cbalint13/e-verest/hardware/everest_v1.5/kicad/e-verest/e-verest.kicad_sch

## KiCad design hardware/everest_v1.5/kicad/e-verest/e-verest.kicad_sch (2021-08-18)

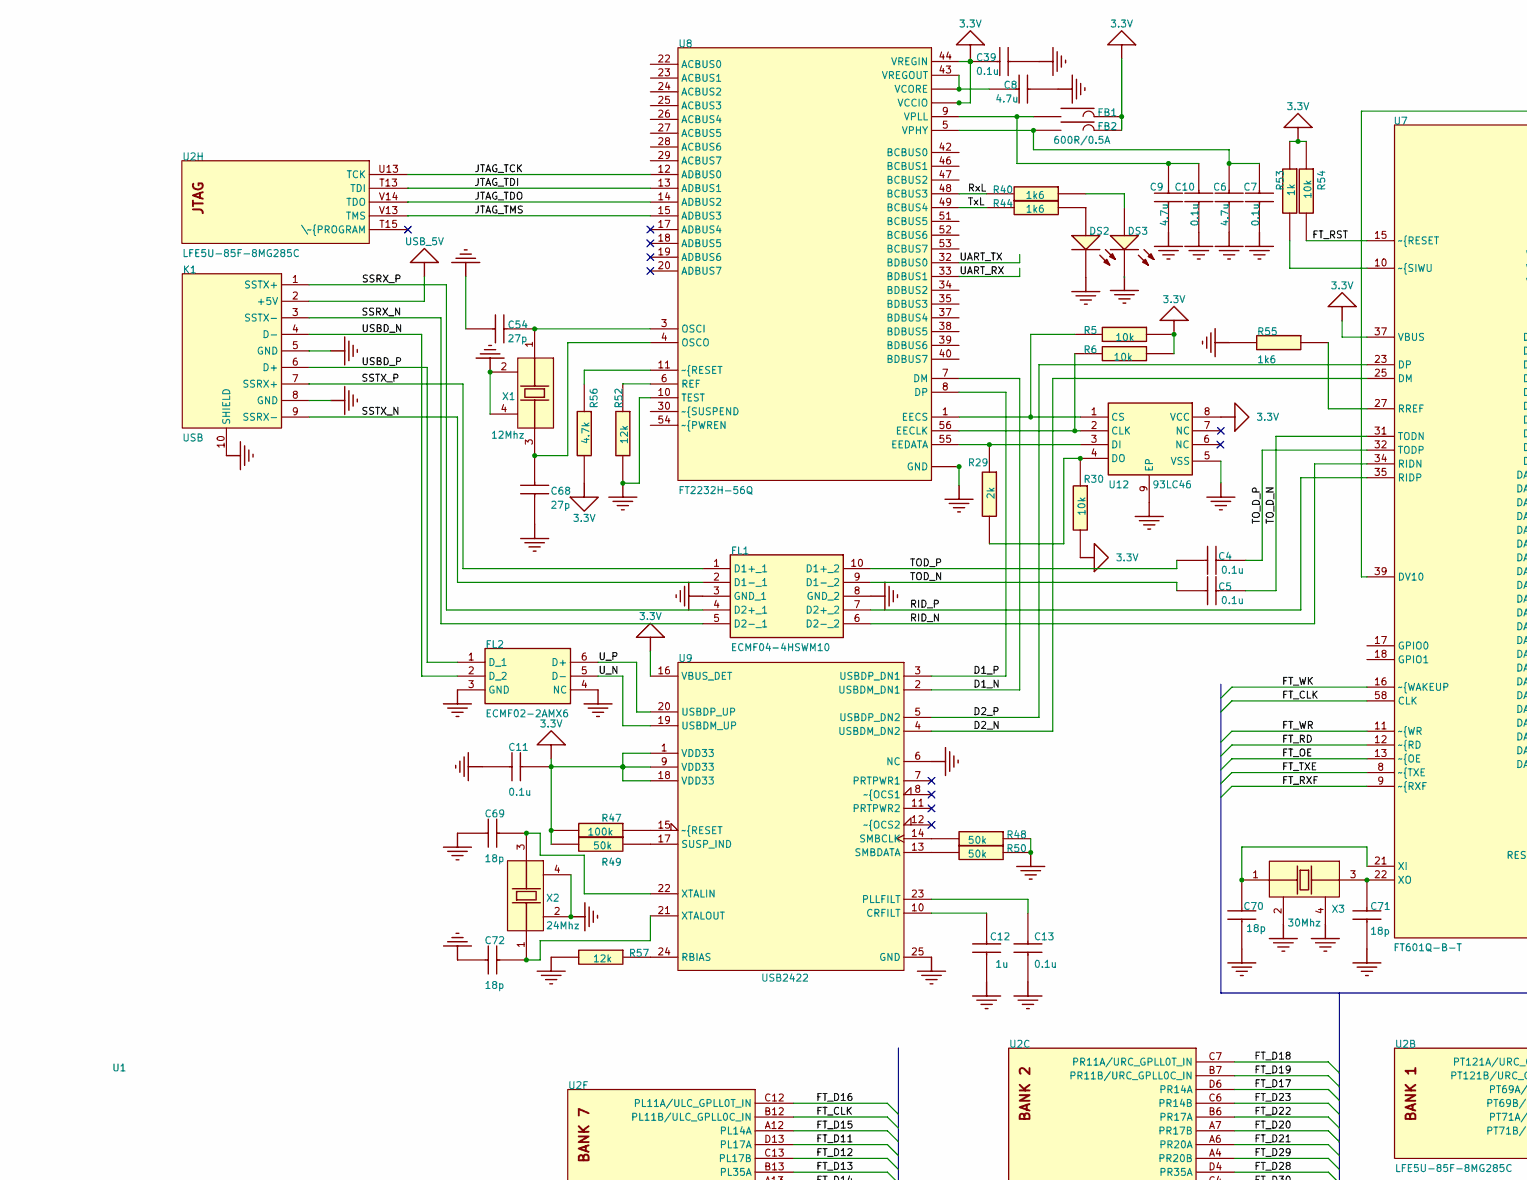
[picture p28: schematic e-verest.kicad_sch, part in row 1, column 1]

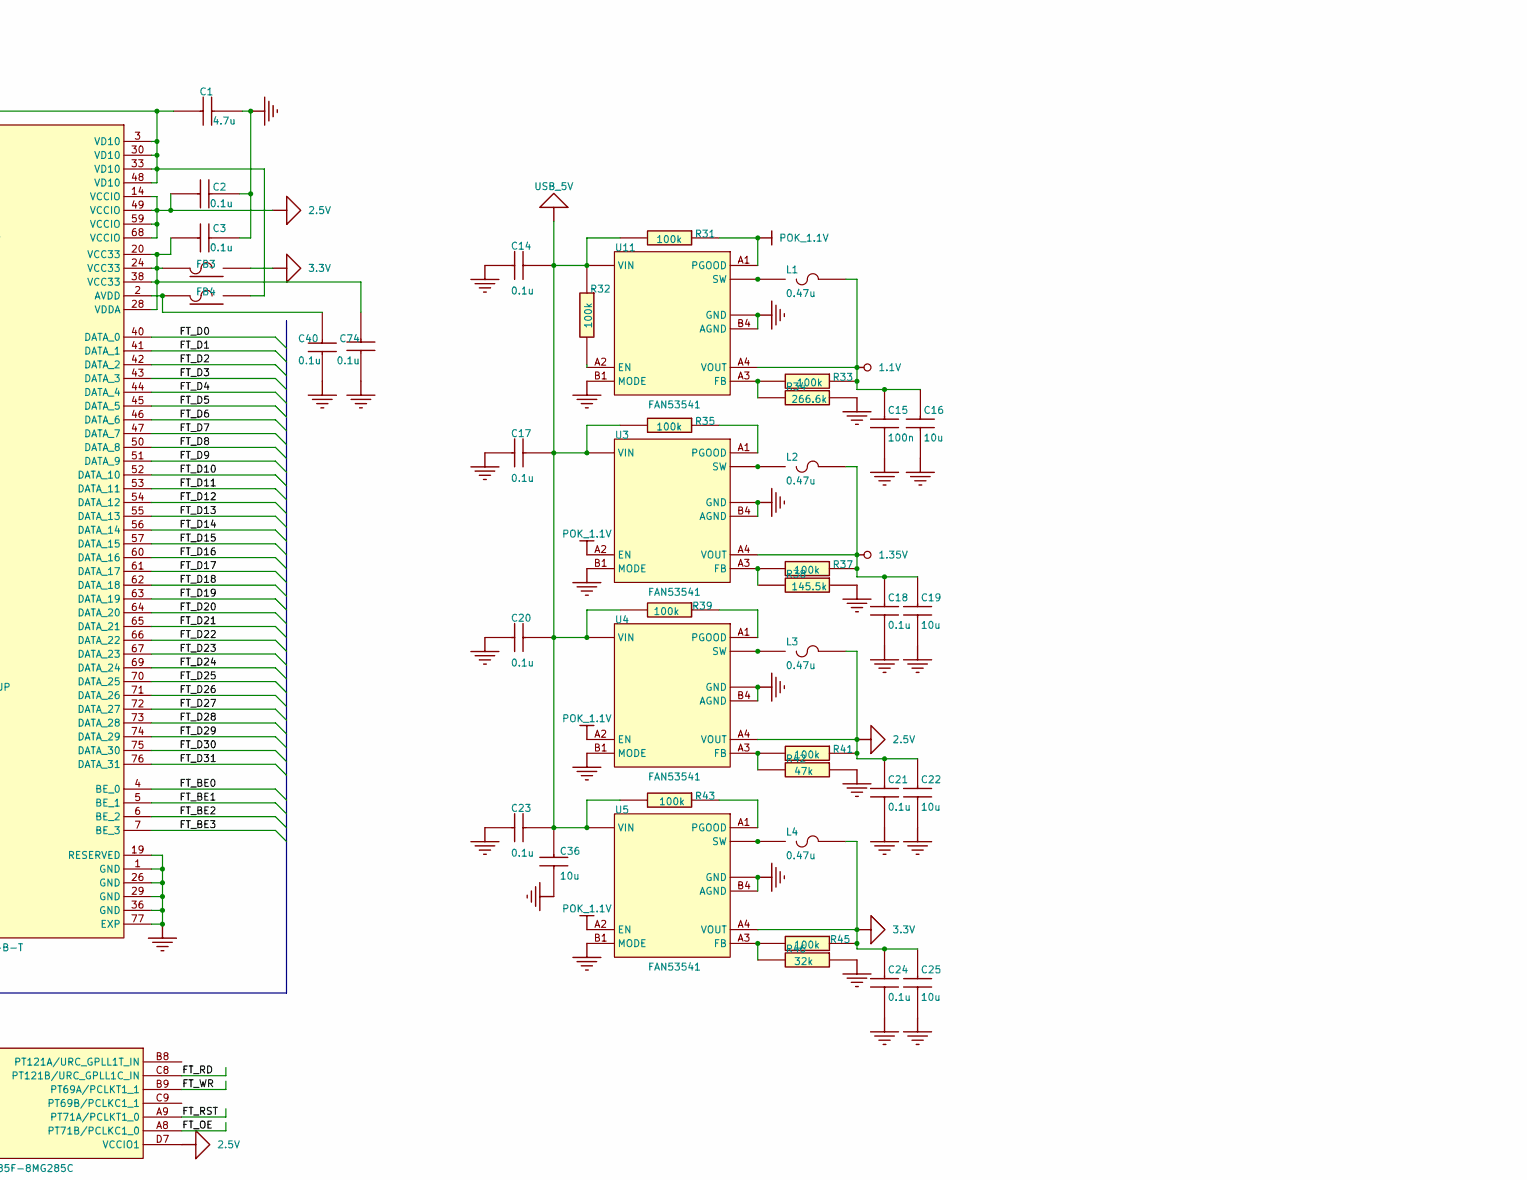
[picture p29: schematic e-verest.kicad_sch, part in row 1, column 2]

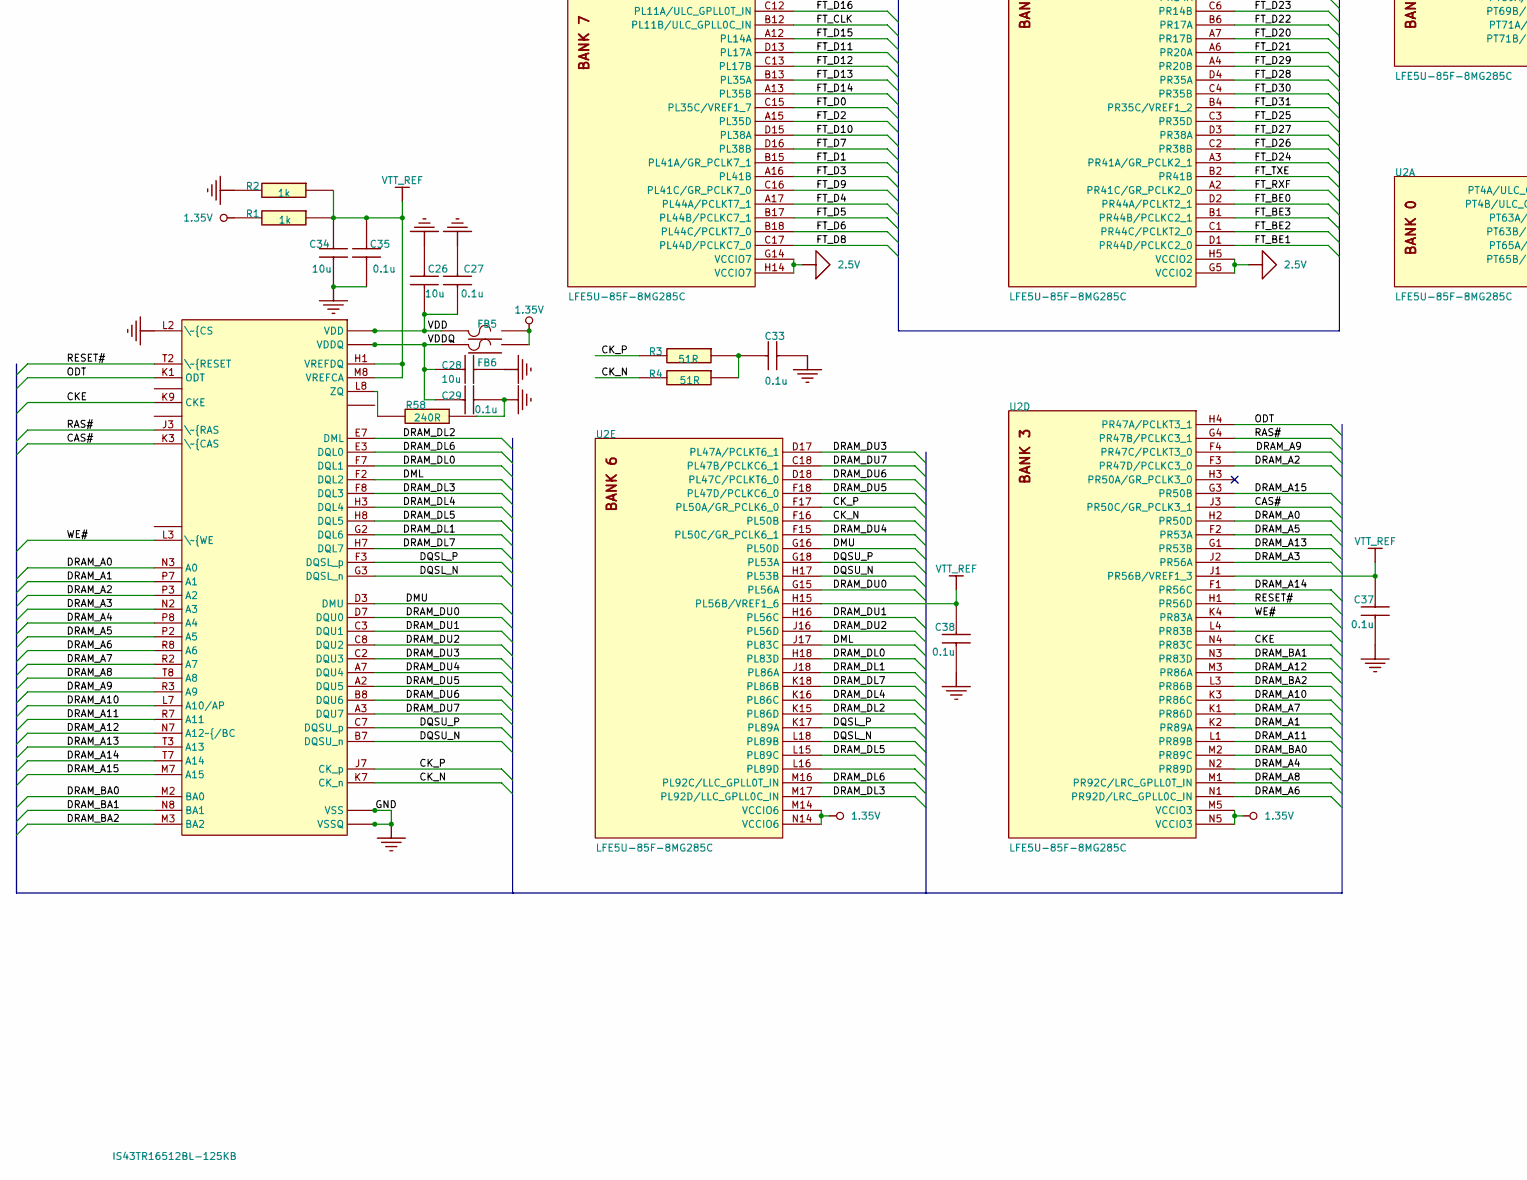
[picture p30: schematic e-verest.kicad_sch, part in row 2, column 1]

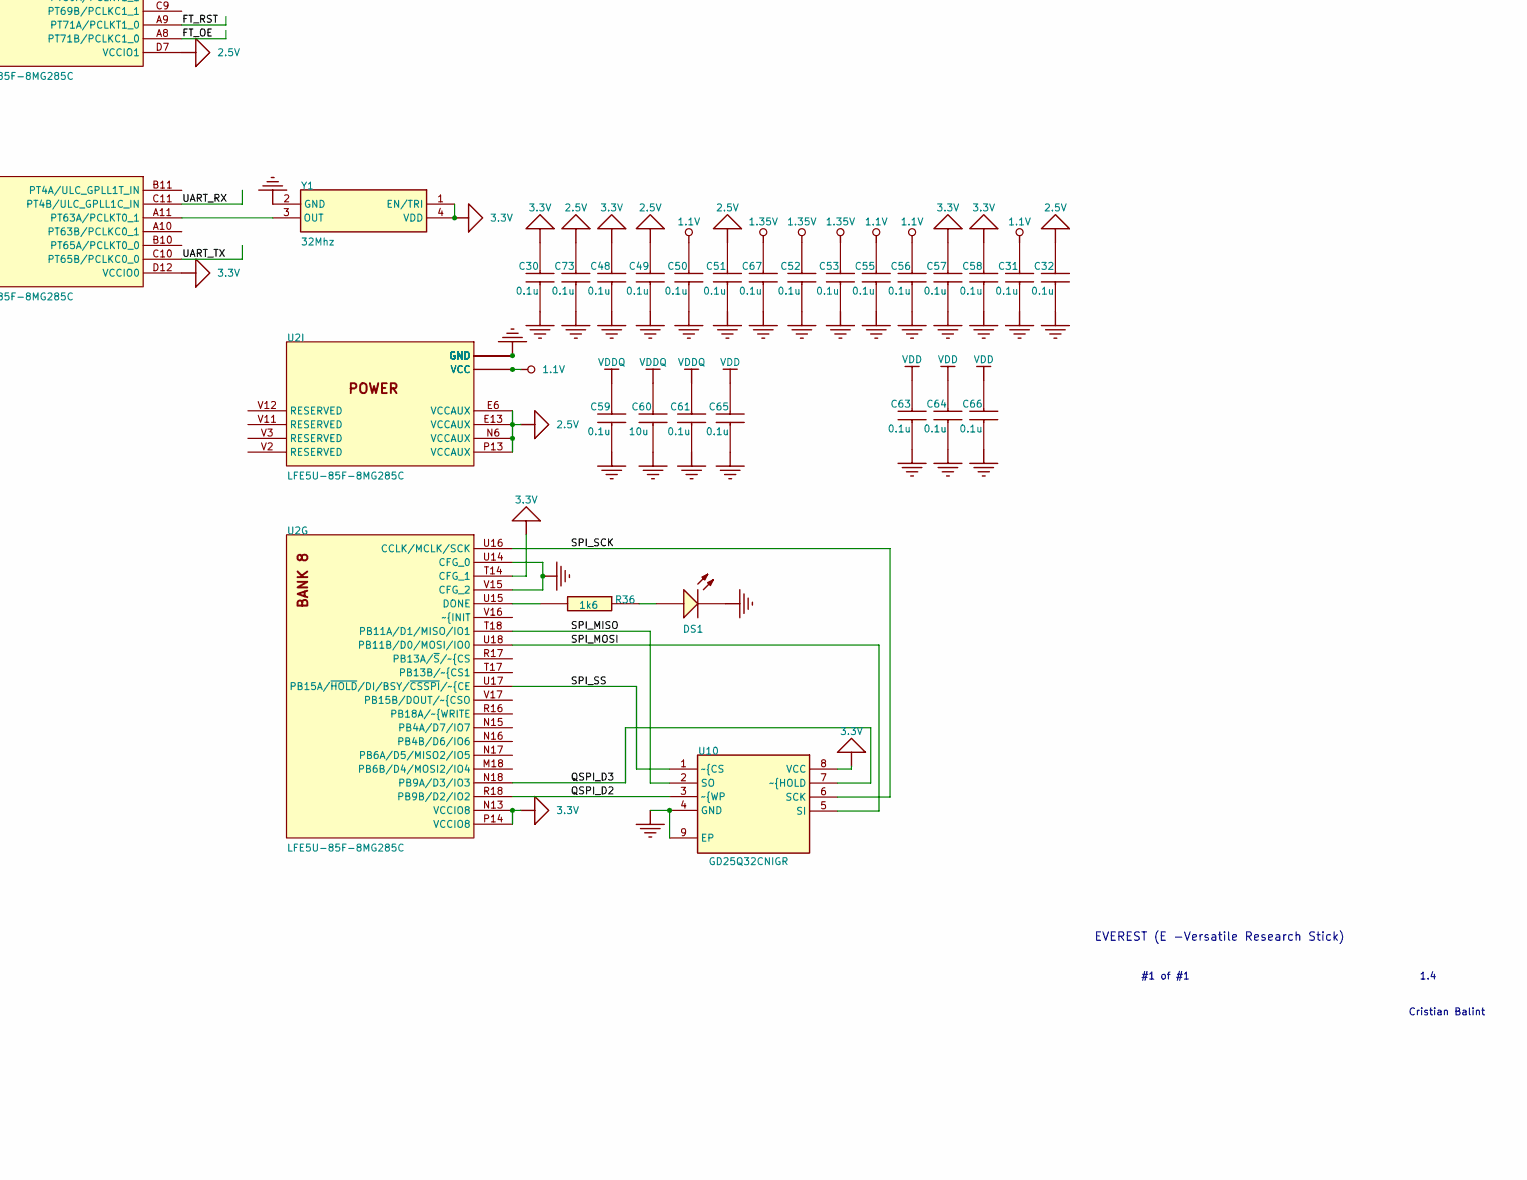
[picture p31: schematic e-verest.kicad_sch, part in row 2, column 2]

Parts:
C1, C6, C8, C9: 4.7u; SMD0201
C2, C3, C4, C5, C7, C10, C11, C13, C14, C17, C18, C20, C21, C23, C24, C30, C31, C33, C37, C39, C48, C49, C51, C52, C53, C55, C56, C57, C58, C63, C67, C73, C74: 0.1u; SMD0201
C12: 1u; SMD0201
C15: 100n; SMD0402
C16, C19, C22, C25, C26, C28, C34, C36, C60: 10u; SMD0402
C27, C29, C32, C35, C38, C40, C50, C59, C61, C64, C65, C66: 0.1u; SMD0402
C54, C68: 27p; SMD0201
C69, C72: 18p; SMD0201
C70, C71: 18p; SMD0402
DS1, DS2, DS3: LED 0603; LED0603
FB1, FB2, FB3, FB4, FB5, FB6: 600R/0.5A; SMD0402
FL1: ECMF04-4HSWM10; SON50P135X260X55-10N-D; MANUFACTURER_PART_NUMBER ECMF04-4HSWM10; MOUSER PART NUMBER 511-ECMF04-4HSWM10
FL2: ECMF02-2AMX6; SON50P150X170X55-6N-D; MANUFACTURER_PART_NUMBER ECMF02-2AMX6; MOUSER PART NUMBER 511-ECMF02-2AMX6
K1: USB; USB-TYPE-A-3.0; MANUFACTURER PART NUMBER 0480370001
L1, L2, L3, L4: 0.47u; SMD0805
R1, R2: 1k; SMD0402
R3, R4: 51R; SMD0201
R5, R6, R30, R54: 10k; SMD0201
R29: 2k; SMD0201
R31, R32, R33, R35, R37, R39, R41, R43, R45, R47: 100k; SMD0201
R34: 266.6k; SMD0201
R36, R40, R44, R55: 1k6; SMD0201
R38: 145.5k; SMD0201
R42: 47k; SMD0201
R46: 32k; SMD0201
R48, R49, R50: 50k; SMD0201
R52, R57: 12k; SMD0201
R53: 1k; SMD0201
R56: 4.7k; SMD0201
R58: 240R; SMD0402
U1: IS43TR16512BL-125KB; *BGA96C80P9X16_1000X1400X140N_IS43TR16512AL-125KBL(Primary)
U2: LFE5U-85F-8MG285C; *BGA285N50P18X18_1000X1000X130
U3, U4, U5, U11: FAN53541; WLCSP20P4X5
U7: FT601Q-B-T; FT601Q
U8: FT2232H-56Q; QFN50P800X800X100-57N-D
U9: USB2422; QFN-MJ24
U10: GD25Q32CNIGR; *SON50P300X400X100-9N
U12: 93LC46; *SON50P200X300X100-9N
X1: 12Mhz; CRYSTAL2520
X2: 24Mhz; CRYSTAL1210
X3: 30Mhz; CRYSTAL1210
Y1: 32Mhz; TY

Connections:
CAS#: U1.K3 (\~{CAS)
CKE: U1.K9 (CKE)
CK_N: R4.2, U1.K7 (CK_n)
CK_P: R3.1, U1.J7 (CK_p)
D1_N: U8.7 (DM), U9.2 (USBDM_DN1)
D1_P: U8.8 (DP), U9.3 (USBDP_DN1)
D2_N: U7.25 (DM), U9.4 (USBDM_DN2)
D2_P: U7.23 (DP), U9.5 (USBDP_DN2)
DML: U1.F2 (DQL2)
DMU: U1.D3 (DMU)
DQSL_N: U1.G3 (DQSL_n), U2.L18 (PL89B)
DQSL_P: U1.F3 (DQSL_p), U2.K17 (PL89A)
DQSU_N: U1.B7 (DQSU_n)
DQSU_P: U1.C7 (DQSU_p)
DRAM_A0: U1.N3 (A0)
DRAM_A1: U1.P7 (A1)
DRAM_A2: U1.P3 (A2)
DRAM_A3: U1.N2 (A3)
DRAM_A4: U1.P8 (A4)
DRAM_A5: U1.P2 (A5)
DRAM_A6: U1.R8 (A6)
DRAM_A7: U1.R2 (A7)
DRAM_A8: U1.T8 (A8)
DRAM_A9: U1.R3 (A9)
DRAM_A10: U1.L7 (A10/AP)
DRAM_A11: U1.R7 (A11)
DRAM_A12: U1.N7 (A12~{/BC)
DRAM_A13: U1.T3 (A13)
DRAM_A14: U1.T7 (A14)
DRAM_A15: U1.M7 (A15)
DRAM_BA0: U1.M2 (BA0)
DRAM_BA1: U1.N8 (BA1), U2.N3 (PR83D)
DRAM_BA2: U1.M3 (BA2)
DRAM_DL0: U1.F7 (DQL1)
DRAM_DL1: U1.G2 (DQL6), U2.J18 (PL86A)
DRAM_DL2: U1.E7 (DML), U2.K15 (PL86D)
DRAM_DL3: U1.F8 (DQL3)
DRAM_DL4: U1.H3 (DQL4), U2.K16 (PL86C)
DRAM_DL5: U1.H8 (DQL5), U2.L15 (PL89C)
DRAM_DL6: U1.E3 (DQL0)
DRAM_DL7: U1.H7 (DQL7), U2.K18 (PL86B)
DRAM_DU0: U1.D7 (DQU0)
DRAM_DU1: U1.C3 (DQU1)
DRAM_DU2: U1.C8 (DQU2)
DRAM_DU3: U1.C2 (DQU3), U2.D17 (PL47A/PCLKT6_1)
DRAM_DU4: U1.A7 (DQU4)
DRAM_DU5: U1.A2 (DQU5), U2.F18 (PL47D/PCLKC6_0)
DRAM_DU6: U1.B8 (DQU6), U2.D18 (PL47C/PCLKT6_0)
DRAM_DU7: U1.A3 (DQU7), U2.C18 (PL47B/PCLKC6_1)
FT_BE0: U7.4 (BE_0)
FT_BE1: U2.D1 (PR44D/PCLKC2_0), U7.5 (BE_1)
FT_BE2: U2.C1 (PR44C/PCLKT2_0), U7.6 (BE_2)
FT_BE3: U7.7 (BE_3)
FT_CLK: U2.B12 (PL11B/ULC_GPLL0C_IN), U7.58 (CLK)
FT_D0: U2.C15 (PL35C/VREF1_7), U7.40 (DATA_0)
FT_D1: U2.B15 (PL41A/GR_PCLK7_1), U7.41 (DATA_1)
FT_D2: U2.A15 (PL35D), U7.42 (DATA_2)
FT_D3: U2.A16 (PL41B), U7.43 (DATA_3)
FT_D4: U2.A17 (PL44A/PCLKT7_1), U7.44 (DATA_4)
FT_D5: U2.B17 (PL44B/PCLKC7_1), U7.45 (DATA_5)
FT_D6: U7.46 (DATA_6)
FT_D7: U2.D16 (PL38B), U7.47 (DATA_7)
FT_D8: U2.C17 (PL44D/PCLKC7_0), U7.50 (DATA_8)
FT_D9: U2.C16 (PL41C/GR_PCLK7_0), U7.51 (DATA_9)
FT_D10: U2.D15 (PL38A), U7.52 (DATA_10)
FT_D11: U2.D13 (PL17A), U7.53 (DATA_11)
FT_D12: U2.C13 (PL17B), U7.54 (DATA_12)
FT_D13: U2.B13 (PL35A), U7.55 (DATA_13)
FT_D14: U2.A13 (PL35B), U7.56 (DATA_14)
FT_D15: U2.A12 (PL14A), U7.57 (DATA_15)
FT_D16: U2.C12 (PL11A/ULC_GPLL0T_IN), U7.60 (DATA_16)
FT_D17: U2.D6 (PR14A), U7.61 (DATA_17)
FT_D18: U2.C7 (PR11A/URC_GPLL0T_IN), U7.62 (DATA_18)
FT_D19: U2.B7 (PR11B/URC_GPLL0C_IN), U7.63 (DATA_19)
FT_D20: U2.A7 (PR17B), U7.64 (DATA_20)
FT_D21: U2.A6 (PR20A), U7.65 (DATA_21)
FT_D22: U2.B6 (PR17A), U7.66 (DATA_22)
FT_D23: U2.C6 (PR14B), U7.67 (DATA_23)
FT_D24: U2.A3 (PR41A/GR_PCLK2_1), U7.69 (DATA_24)
FT_D25: U2.C3 (PR35D), U7.70 (DATA_25)
FT_D26: U2.C2 (PR38B), U7.71 (DATA_26)
FT_D27: U2.D3 (PR38A), U7.72 (DATA_27)
FT_D28: U2.D4 (PR35A), U7.73 (DATA_28)
FT_D29: U2.A4 (PR20B), U7.74 (DATA_29)
FT_D30: U2.C4 (PR35B), U7.75 (DATA_30)
FT_D31: U2.B4 (PR35C/VREF1_2), U7.76 (DATA_31)
FT_OE: U2.A8 (PT71B/PCLKC1_0), U7.13 (~{OE)
FT_RD: U2.C8 (PT121B/URC_GPLL1C_IN), U7.12 (~{RD)
FT_RST: R54.2, U2.A9 (PT71A/PCLKT1_0), U7.15 (~{RESET)
FT_RXF: U7.9 (~{RXF)
FT_TXE: U2.B2 (PR41B), U7.8 (~{TXE)
FT_WK: U7.16 (~{WAKEUP)
FT_WR: U2.B9 (PT69A/PCLKT1_1), U7.11 (~{WR)
GND: U1.A9 (VSS), U1.B1 (VSSQ), U1.B3 (VSS), U1.B9 (VSSQ), U1.D1 (VSSQ), U1.D8 (VSSQ), U1.E1 (VSS), U1.E2 (VSSQ), U1.E8 (VSSQ), U1.F9 (VSSQ), U1.G1 (VSSQ), U1.G8 (VSS), U1.G9 (VSSQ), U1.J2 (VSS), U1.J8 (VSS), U1.M1 (VSS), U1.M9 (VSS), U1.P1 (VSS), U1.P9 (VSS), U1.T1 (VSS), U1.T9 (VSS)
JTAG_TCK: U2.U13 (TCK), U8.12 (ADBUS0)
JTAG_TDI: U2.T13 (TDI)
JTAG_TDO: U2.V14 (TDO)
JTAG_TMS: U2.V13 (TMS)
unnamed: C1.1, C2.1, C3.1
unnamed: C1.2, FB4.1, U7.3 (VD10), U7.30 (VD10), U7.33 (VD10), U7.39 (DV10), U7.48 (VD10)
unnamed: C2.2, U7.14 (VCCIO), U7.49 (VCCIO), U7.59 (VCCIO), U7.68 (VCCIO)
unnamed: C3.2, C74.2, U7.20 (VCC33), U7.24 (VCC33), U7.28 (VDDA), U7.38 (VCC33)
unnamed: C11.1, R47.1, R49.1, U9.1 (VDD33), U9.9 (VDD33), U9.18 (VDD33)
unnamed: C12.1, U9.10 (CRFILT)
unnamed: C13.1, U9.23 (PLLFILT)
unnamed: C14.1, C17.1, C20.1, C23.1, C36.2, R31.1, R32.2, R35.1, R39.1, R43.1, U3.D1 (VIN), U3.D2 (VIN), U3.E1 (VIN), U3.E2 (VIN), U4.D1 (VIN), U4.D2 (VIN), U4.E1 (VIN), U4.E2 (VIN), U5.D1 (VIN), U5.D2 (VIN), U5.E1 (VIN), U5.E2 (VIN), U11.D1 (VIN), U11.D2 (VIN), U11.E1 (VIN), U11.E2 (VIN)
unnamed: C15.2, C16.2, L1.2, R33.2, U11.A4 (VOUT)
unnamed: C18.2, C19.2, L2.2, R37.2
unnamed: C24.2, C25.2, L4.2, R45.2, U5.A4 (VOUT)
unnamed: C29.1, R58.2
unnamed: C33.2, R4.1
unnamed: C34.1, C35.1, U1.H1 (VREFDQ), U1.M8 (VREFCA)
unnamed: C40.1, U7.2 (AVDD)
unnamed: C54.1, U8.3 (OSCI), X1.1 (X1)
unnamed: C69.2, U9.22 (XTALIN), X2.3 (X2)
unnamed: C70.1, U7.21 (XI), X3.1 (X1)
unnamed: C71.1, U7.22 (XO), X3.3 (X2)
unnamed: C72.2, U9.21 (XTALOUT), X2.1 (X1)
unnamed: DS1.1 (A), R36.1
unnamed: DS2.1 (A), R44.1
unnamed: DS3.1 (A), R40.1
unnamed: FB1.1, U8.9 (VPLL)
unnamed: FB1.2, FB2.2
unnamed: FB2.1, U8.5 (VPHY)
unnamed: FB5.1, FB6.1
unnamed: FL1.1 (D1+_1), K1.7 (SSRX+)
unnamed: L1.1, U11.D3 (SW), U11.D4 (SW), U11.E3 (SW), U11.E4 (SW)
unnamed: L2.1, U3.D3 (SW), U3.D4 (SW), U3.E3 (SW), U3.E4 (SW)
unnamed: L3.1, U4.D3 (SW), U4.D4 (SW), U4.E3 (SW), U4.E4 (SW)
unnamed: L3.2, R41.2, U4.A4 (VOUT)
unnamed: L4.1, U5.D3 (SW), U5.D4 (SW), U5.E3 (SW), U5.E4 (SW)
unnamed: R5.1, U8.1 (EECS), U12.1 (CS)
unnamed: R5.2, R6.2
unnamed: R6.1, U8.56 (EECLK), U12.2 (CLK)
unnamed: R29.1, U8.55 (EEDATA), U12.3 (DI)
unnamed: R29.2, R30.1, U12.4 (DO)
unnamed: R32.1, U11.A2 (EN)
unnamed: R33.1, U11.A3 (FB)
unnamed: R41.1, U4.A3 (FB)
unnamed: R45.1, U5.A3 (FB)
unnamed: R47.2, U9.15 (~{RESET)
unnamed: R48.1, U9.14 (SMBCLK)
unnamed: R49.2, U9.17 (SUSP_IND)
unnamed: R50.1, U9.13 (SMBDATA)
unnamed: R52.1, U8.10 (TEST)
unnamed: R53.1, R54.1
unnamed: R53.2, U7.10 (~{SIWU)
unnamed: R55.1, U7.27 (RREF)
unnamed: R56.2, U8.11 (~{RESET)
unnamed: R57.2, U9.24 (RBIAS)
unnamed: R58.1, U1.L8 (ZQ)
unnamed: U2.A11 (PT63A/PCLKT0_1), Y1.3 (OUT)
unnamed: U2.B3 (GND), U2.B16 (GND), U2.E5 (GND), U2.E7 (GND), U2.E8 (GND), U2.E9 (GND), U2.E10 (GND), U2.E11 (GND), U2.E12 (GND), U2.E14 (GND), U2.F5 (GND), U2.F6 (GND), U2.F7 (GND), U2.F8 (GND), U2.F9 (GND), U2.F10 (GND), U2.F11 (GND), U2.F12 (GND), U2.F13 (GND), U2.F14 (GND), U2.G2 (GND), U2.G6 (GND), U2.G7 (GND), U2.G8 (GND), U2.G9 (GND), U2.G10 (GND), U2.G11 (GND), U2.G13 (GND), U2.G17 (GND), U2.H7 (GND), U2.H8 (GND), U2.H9 (GND), U2.H10 (GND), U2.H11 (GND), U2.H12 (GND), U2.H13 (GND), U2.J6 (GND), U2.J7 (GND), U2.J8 (GND), U2.J9 (GND), U2.J10 (GND), U2.J11 (GND), U2.J12 (GND), U2.J13 (GND), U2.K5 (GND), U2.K6 (GND), U2.K7 (GND), U2.K8 (GND), U2.K9 (GND), U2.K10 (GND), U2.K11 (GND), U2.K12 (GND), U2.K13 (GND), U2.L2 (GND), U2.L5 (GND), U2.L6 (GND), U2.L7 (GND), U2.L8 (GND), U2.L9 (GND), U2.L10 (GND), U2.L11 (GND), U2.L12 (GND), U2.L13 (GND), U2.L14 (GND), U2.M6 (GND), U2.M7 (GND), U2.M8 (GND), U2.M9 (GND), U2.M10 (GND), U2.M11 (GND), U2.M13 (GND), U2.N7 (GND), U2.N8 (GND), U2.N9 (GND), U2.N10 (GND), U2.N11 (GND), U2.N12 (GND), U2.P5 (GND), U2.P8 (GND), U2.P10 (GND), U2.P12 (GND), U2.R1 (GND), U2.R2 (GND), U2.R3 (GND), U2.R10 (GND), U2.T1 (GND), U2.T2 (GND), U2.T4 (GND), U2.T5 (GND), U2.T6 (GND), U2.T7 (GND), U2.T8 (GND), U2.T9 (GND), U2.T10 (GND), U2.T12 (GND), U2.T16 (GND), U2.U1 (GND), U2.U2 (GND), U2.U4 (GND), U2.U5 (GND), U2.U6 (GND), U2.U7 (GND), U2.U8 (GND), U2.U9 (GND), U2.U10 (GND), U2.U11 (GND), U2.U12 (GND), U2.V4 (GND), U2.V5 (GND), U2.V6 (GND), U2.V7 (GND), U2.V8 (GND), U2.V9 (GND), U2.V10 (GND)
unnamed: U2.D8 (VCC), U2.D9 (VCC), U2.D10 (VCC), U2.D11 (VCC), U2.J4 (VCC), U2.J5 (VCC), U2.J15 (VCC), U2.M4 (VCC), U2.M15 (VCC), U2.P7 (VCC), U2.P9 (VCC), U2.P11 (VCC)
unnamed: U2.G5 (VCCIO2), U2.H5 (VCCIO2)
unnamed: U2.G14 (VCCIO7), U2.H14 (VCCIO7)
unnamed: U2.N13 (VCCIO8), U2.P14 (VCCIO8)
unnamed: U2.T11 (GND), U2.U3 (GND)
unnamed: U2.U14 (CFG_0), U2.V15 (CFG_2)
unnamed: U3.B2 (GND), U3.B3 (GND), U3.C1 (GND), U3.C2 (GND), U3.C3 (GND), U3.C4 (GND)
unnamed: U4.B2 (GND), U4.B3 (GND), U4.B4 (AGND), U4.C1 (GND), U4.C2 (GND), U4.C3 (GND), U4.C4 (GND)
unnamed: U5.B2 (GND), U5.B3 (GND), U5.B4 (AGND), U5.C1 (GND), U5.C2 (GND), U5.C3 (GND), U5.C4 (GND)
unnamed: U7.1 (GND), U7.19 (RESERVED), U7.26 (GND), U7.29 (GND), U7.36 (GND), U7.77 (EXP)
unnamed: U8.2 (VCORE), U8.31 (VCORE), U8.43 (VREGOUT)
unnamed: U8.4 (OSCO), X1.3 (X2)
unnamed: U8.16 (VCCIO), U8.36 (VCCIO), U8.44 (VREGIN), U8.50 (VCCIO)
unnamed: U8.21 (GND), U8.41 (GND), U8.45 (GND), U8.57 (GND)
unnamed: U2.U17 (PB15A/~HOLD/DI/BSY/~CSSPI/~{CE), U10.1 (~{CS)
unnamed: U10.4 (GND), U10.9 (EP)
unnamed: U11.B2 (GND), U11.B3 (GND), U11.B4 (AGND), U11.C1 (GND), U11.C2 (GND), U11.C3 (GND), U11.C4 (GND)
unnamed: X1.2 (GND), X1.4 (GND)
unnamed: X2.2 (GND), X2.4 (GND)
unnamed: Y1.1 (EN/TRI), Y1.4 (VDD)
ODT: U1.K1 (ODT), U2.H4 (PR47A/PCLKT3_1)
QSPI_D2: U2.R18 (PB9B/D2/IO2), U10.3 (~{WP)
QSPI_D3: U2.N18 (PB9A/D3/IO3), U10.7 (~{HOLD)
RAS#: U1.J3 (\~{RAS), U2.G4 (PR47B/PCLKC3_1)
RESET#: U1.T2 (\~{RESET)
RID_N: FL1.6 (D2-_2), U7.34 (RIDN)
RID_P: FL1.7 (D2+_2), U7.35 (RIDP)
RxL: R40.2, U8.48 (BCBUS3)
SPI_MISO: U2.T18 (PB11A/D1/MISO/IO1), U10.2 (SO)
SPI_MOSI: U2.U18 (PB11B/D0/MOSI/IO0), U10.5 (SI)
SPI_SCK: U2.U16 (CCLK/MCLK/SCK), U10.6 (SCK)
SSRX_N: FL1.5 (D2-_1), K1.3 (SSTX-)
SSRX_P: FL1.4 (D2+_1), K1.1 (SSTX+)
SSTX_N: FL1.2 (D1-_1), K1.9 (SSRX-)
TOD_N: C5.1, FL1.9 (D1-_2)
TOD_P: C4.1, FL1.10 (D1+_2)
TO_D_N: U7.31 (TODN)
TO_D_P: U7.32 (TODP)
TxL: R44.2, U8.49 (BCBUS4)
UART_RX: U2.C11 (PT4B/ULC_GPLL1C_IN), U8.33 (BDBUS1)
UART_TX: U8.32 (BDBUS0)
USBD_N: FL2.2 (D_2), K1.4 (D-)
USBD_P: FL2.1 (D_1), K1.6 (D+)
U_N: FL2.5 (D-), U9.19 (USBDM_UP)
U_P: FL2.6 (D+), U9.20 (USBDP_UP)
VDD: C26.2, C27.2, FB5.2, U1.B2 (VDD), U1.D9 (VDD), U1.G7 (VDD), U1.K2 (VDD), U1.K8 (VDD), U1.N1 (VDD), U1.N9 (VDD), U1.R1 (VDD), U1.R9 (VDD)
VDDQ: C28.2, C29.2, FB6.2, U1.A1 (VDDQ), U1.A8 (VDDQ), U1.C1 (VDDQ), U1.C9 (VDDQ), U1.D2 (VDDQ), U1.E9 (VDDQ), U1.F1 (VDDQ), U1.H2 (VDDQ), U1.H9 (VDDQ)
WE#: U1.L3 (\~{WE)

Notes on the sheet:
EVEREST (E -Versatile Research Stick)
#1 of #1
Cristian Balint
1.4
