cbalint13/e-verest/utils/test-firmware/rtl/pll.v

module pll_32_50 (
    input clki, // 32 MHz, 0 deg
    output clko // 49.7778 MHz, 0 deg
);
(* FREQUENCY_PIN_CLKI="32" *)
(* FREQUENCY_PIN_CLKOP="49.7778" *)
(* ICP_CURRENT="12" *) (* LPF_RESISTOR="8" *) (* MFG_ENABLE_FILTEROPAMP="1" *) (* MFG_GMCREF_SEL="2" *)
EHXPLLL #(
        .PLLRST_ENA("DISABLED"),
        .INTFB_WAKE("DISABLED"),
        .STDBY_ENABLE("DISABLED"),
        .DPHASE_SOURCE("DISABLED"),
        .OUTDIVIDER_MUXA("DIVA"),
        .OUTDIVIDER_MUXB("DIVB"),
        .OUTDIVIDER_MUXC("DIVC"),
        .OUTDIVIDER_MUXD("DIVD"),
        .CLKI_DIV(9),
        .CLKOP_ENABLE("ENABLED"),
        .CLKOP_DIV(12),
        .CLKOP_CPHASE(5),
        .CLKOP_FPHASE(0),
        .FEEDBK_PATH("CLKOP"),
        .CLKFB_DIV(14)
    ) pll_i (
        .RST(1'b0),
        .STDBY(1'b0),
        .CLKI(clki),
        .CLKOP(clko),
        .CLKFB(clko),
        .CLKINTFB(),
        .PHASESEL0(1'b0),
        .PHASESEL1(1'b0),
        .PHASEDIR(1'b1),
        .PHASESTEP(1'b1),
        .PHASELOADREG(1'b1),
        .PLLWAKESYNC(1'b0),
        .ENCLKOP(1'b0),
);
endmodule

module pll_100_50 (
    input clki, // 100 MHz, 0 deg
    output clko // 50 MHz, 0 deg
);
(* FREQUENCY_PIN_CLKI="100" *)
(* FREQUENCY_PIN_CLKOP="50" *)
(* ICP_CURRENT="12" *) (* LPF_RESISTOR="8" *) (* MFG_ENABLE_FILTEROPAMP="1" *) (* MFG_GMCREF_SEL="2" *)
EHXPLLL #(
        .PLLRST_ENA("DISABLED"),
        .INTFB_WAKE("DISABLED"),
        .STDBY_ENABLE("DISABLED"),
        .DPHASE_SOURCE("DISABLED"),
        .OUTDIVIDER_MUXA("DIVA"),
        .OUTDIVIDER_MUXB("DIVB"),
        .OUTDIVIDER_MUXC("DIVC"),
        .OUTDIVIDER_MUXD("DIVD"),
        .CLKI_DIV(2),
        .CLKOP_ENABLE("ENABLED"),
        .CLKOP_DIV(12),
        .CLKOP_CPHASE(5),
        .CLKOP_FPHASE(0),
        .FEEDBK_PATH("CLKOP"),
        .CLKFB_DIV(1)
    ) pll_i (
        .RST(1'b0),
        .STDBY(1'b0),
        .CLKI(clki),
        .CLKOP(clko),
        .CLKFB(clko),
        .CLKINTFB(),
        .PHASESEL0(1'b0),
        .PHASESEL1(1'b0),
        .PHASEDIR(1'b1),
        .PHASESTEP(1'b1),
        .PHASELOADREG(1'b1),
        .PLLWAKESYNC(1'b0),
        .ENCLKOP(1'b0),
);
endmodule
